visrealm/keyboard4a99/doc/img/base-off.jpg

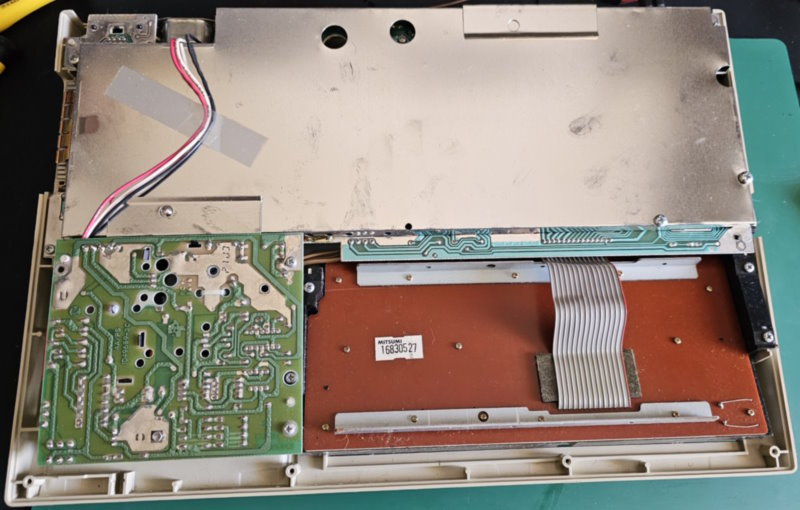
doc/img/base-off.jpg
