visrealm/keyboard4a99/doc/img/threaded-inserts.jpg

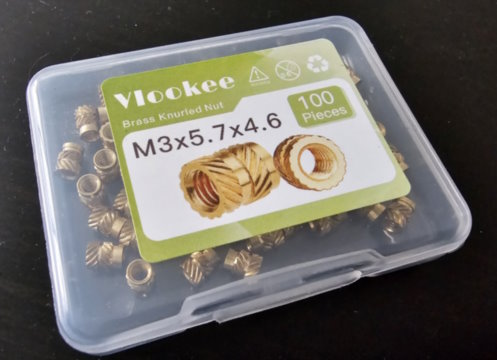
doc/img/threaded-inserts.jpg
